zargony/touch-n-drink/firmware/esp32/src/buzzer.rs

use derive_more::{Display, From};
use embassy_time::Timer;
use esp_hal::gpio::{AnyPin, DriveMode, OutputPin};
use esp_hal::ledc::channel::{self, ChannelIFace};
use esp_hal::ledc::timer::{self, TimerIFace};
use esp_hal::ledc::{LSGlobalClkSource, Ledc, LowSpeed};
use esp_hal::peripherals::LEDC;
use esp_hal::time::Rate;
use log::{debug, info};

/// PWM duty cycle to use for tones (percentage, 0-100)
/// For an active low buzzer, 75% duty cycle means 25% active time.
/// 50% produces max volume, 100% is off
#[cfg(not(debug_assertions))]
const TONE_DUTY_CYCLE: u8 = 75;
#[cfg(debug_assertions)]
const TONE_DUTY_CYCLE: u8 = 97;

/// Buzzer error
#[derive(Debug, Display, From)]
pub enum Error {
    /// PWM timer error
    #[display("PWM timer error")]
    Timer(timer::Error),
    /// PWM channel error
    #[display("PWM channel error")]
    Channel(channel::Error),
}

/// Passive buzzer (driven by PWM signal on GPIO)
pub struct Buzzer<'a> {
    ledc: Ledc<'a>,
    pin: AnyPin<'a>,
}

impl common::Buzzer for Buzzer<'_> {
    async fn tone(&mut self, frequency: u32, duration: u64) {
        let _ = self.tone(frequency, duration).await;
    }
}

impl<'a> Buzzer<'a> {
    /// Create new buzzer driver
    pub fn new(ledc: LEDC<'a>, pin: impl OutputPin + 'a) -> Self {
        debug!("Buzzer: Initializing PWM controller...");

        let mut ledc = Ledc::new(ledc);
        ledc.set_global_slow_clock(LSGlobalClkSource::APBClk);

        info!("Buzzer: PWM controller initialized");
        Self {
            ledc,
            pin: pin.degrade(),
        }
    }

    /// Drive the buzzer with a PWM signal of given frequency and duty cycle
    fn drive(&mut self, frequency: u32, duty_pct: u8) -> Result<(), Error> {
        // debug!("Buzzer: driving {frequency} Hz at {duty_pct}%");
        let mut lstimer0 = self.ledc.timer::<LowSpeed>(timer::Number::Timer0);
        lstimer0.configure(timer::config::Config {
            duty: timer::config::Duty::Duty13Bit,
            clock_source: timer::LSClockSource::APBClk,
            frequency: Rate::from_hz(frequency),
        })?;
        let mut channel0 = self
            .ledc
            .channel(channel::Number::Channel0, self.pin.reborrow());
        channel0.configure(channel::config::Config {
            timer: &lstimer0,
            duty_pct,
            drive_mode: DriveMode::PushPull,
        })?;
        Ok(())
    }

    /// Stop driving the buzzer
    #[expect(clippy::unused_self, clippy::unnecessary_wraps)]
    pub fn off(&mut self) -> Result<(), Error> {
        // debug!("Buzzer: turning off");
        // Turn off buzzer by disabling LEDC signal output, keep the output high
        // FIXME: Unfortunately, esp-hal doesn't provide methods, so we modify registers directly
        #[rustfmt::skip]
        LEDC::regs().ch(0).conf0().modify(|_, w| w
            .sig_out_en().clear_bit()
            .idle_lv().set_bit()
            .para_up().set_bit()
        );
        #[rustfmt::skip]
        LEDC::regs().timer(0).conf().modify(|_, w| w
            .pause().set_bit()
            .rst().set_bit()
            .para_up().set_bit()
        );
        Ok(())
    }

    /// Output the given tone for given duration
    pub async fn tone(&mut self, frequency: u32, duration: u64) -> Result<(), Error> {
        // debug!("Buzzer: playing {frequency} Hz for {duration} ms");
        self.drive(frequency, TONE_DUTY_CYCLE)?;
        Timer::after_millis(duration).await;
        self.off()?;
        Ok(())
    }
}
